nathanpower1/3D_Printed_Spectrometer/New Spectrometer Spectral Pics/mercury new spec 3.png

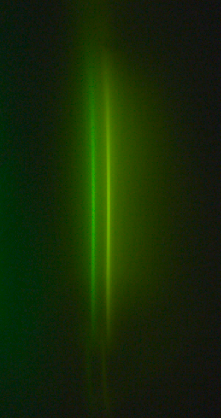
New Spectrometer Spectral Pics/mercury new spec 3.png
