nathanpower1/3D_Printed_Spectrometer/New Spectrometer Spectral Pics/mercury new spectometer.png

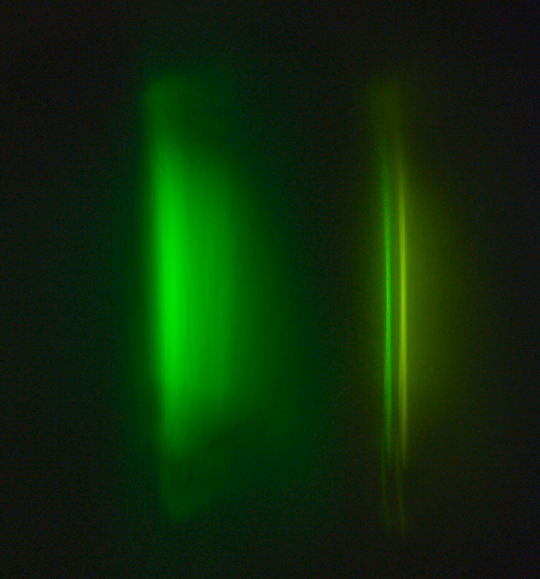
New Spectrometer Spectral Pics/mercury new spectometer.png
