nathanpower1/3D_Printed_Spectrometer/New Spectrometer Spectral Pics/Mercury Plot New.png

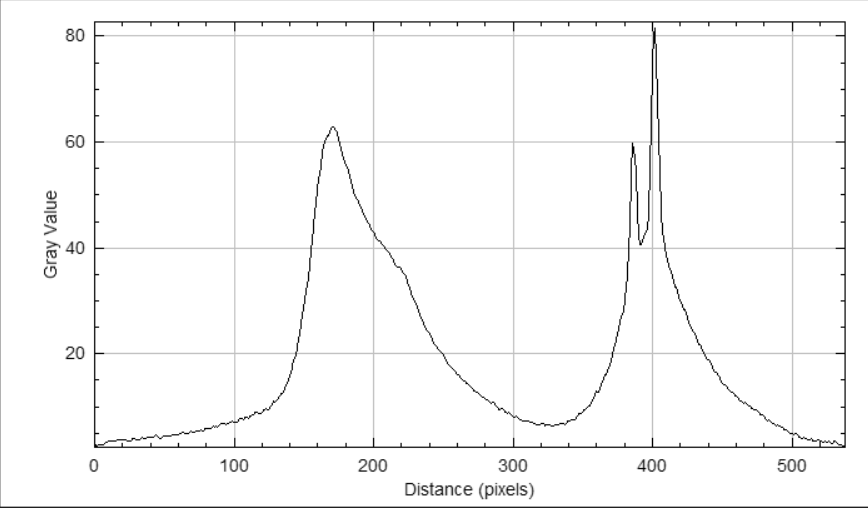
New Spectrometer Spectral Pics/Mercury Plot New.png
