nathanpower1/3D_Printed_Spectrometer/New Spectrometer Spectral Pics/neon new spec 2.png

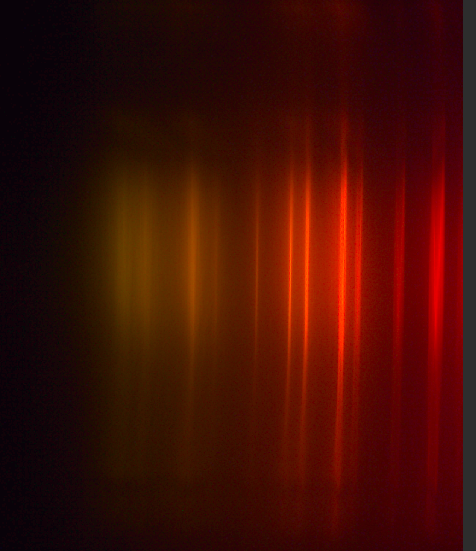
New Spectrometer Spectral Pics/neon new spec 2.png
