nathanpower1/3D_Printed_Spectrometer/New Spectrometer Spectral Pics/neon new spec.png

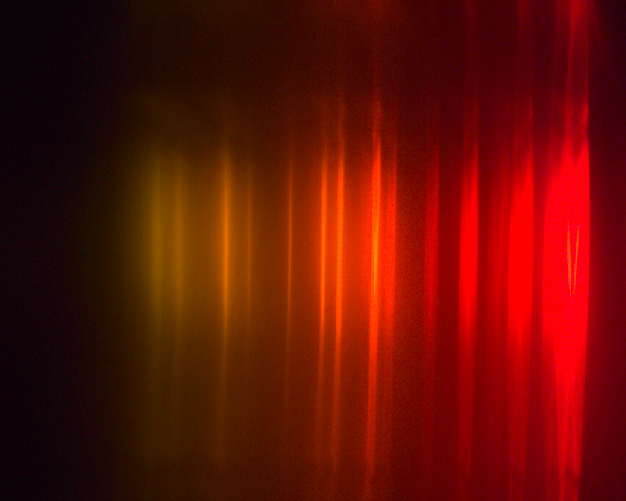
New Spectrometer Spectral Pics/neon new spec.png
