nathanpower1/3D_Printed_Spectrometer/New Spectrometer Spectral Pics/Neon Plot New.png

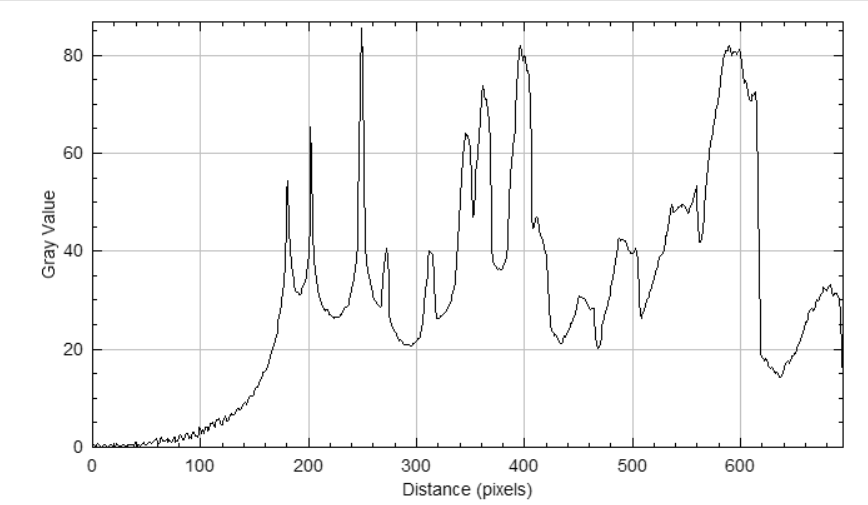
New Spectrometer Spectral Pics/Neon Plot New.png
