nathanpower1/3D_Printed_Spectrometer/New Spectrometer Spectral Pics/sodium doublet new spec 2.png

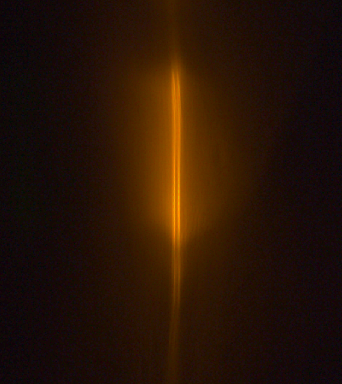
New Spectrometer Spectral Pics/sodium doublet new spec 2.png
