nathanpower1/3D_Printed_Spectrometer/3D Printer Files/SlitFiles/FixedBlade.stl

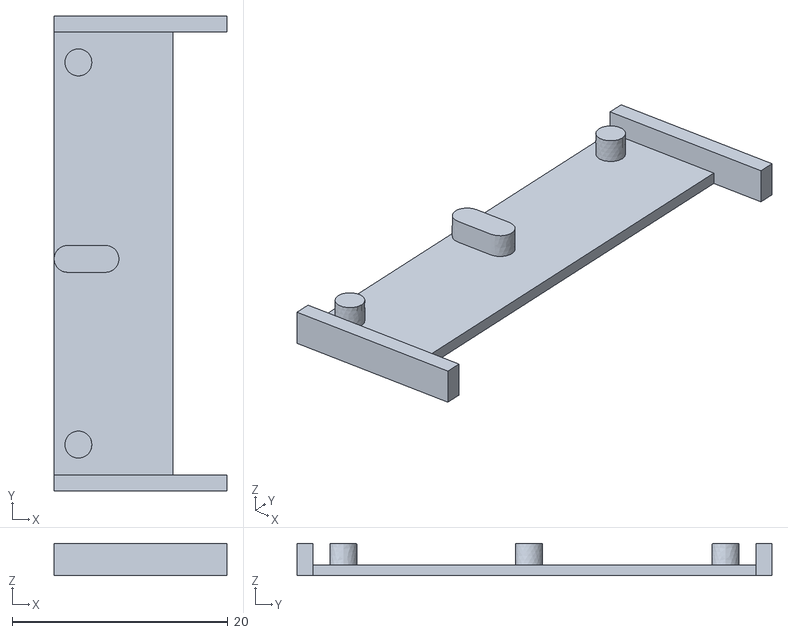
[picture p31: CAD file, 2024-04-24]
3D Printer Files/SlitFiles/FixedBlade.stl
16.0 x 44.0 x 3.00
