nathanpower1/3D_Printed_Spectrometer/3D Printer Files/CamFiles/Camera v2.stl

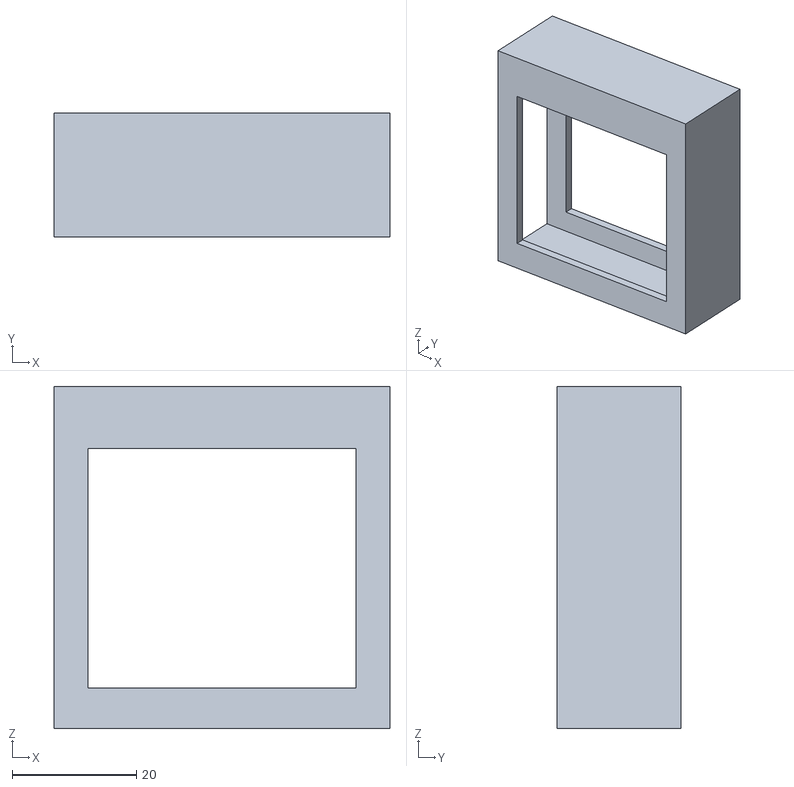
[picture p32: CAD file, 2024-04-24]
3D Printer Files/CamFiles/Camera v2.stl
54.0 x 20.0 x 55.0
