nathanpower1/3D_Printed_Spectrometer/3D Printer Files/Lens CAD file/Customizable_Optical_Lens_Holder_3359613/files/lense_holder_110x18.stl

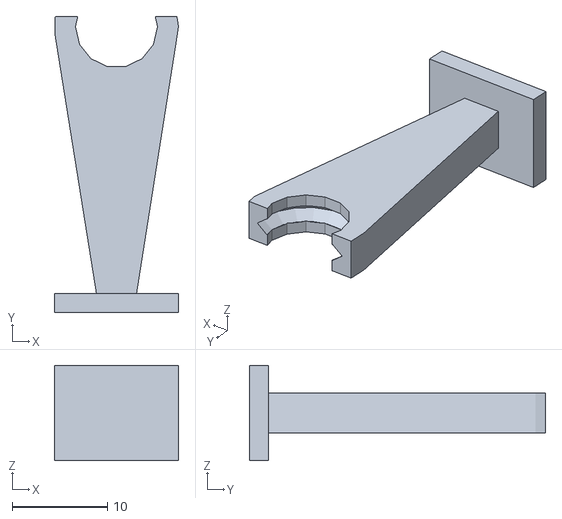
[picture p33: CAD file, 2024-04-24]
3D Printer Files/Lens CAD file/Customizable_Optical_Lens_Holder_3359613/files/lense_holder_110x18.stl
13.0 x 31.1 x 10.0
