nathanpower1/3D_Printed_Spectrometer/3D Printer Files/CamFiles/Case v1 Nathan Power.stl

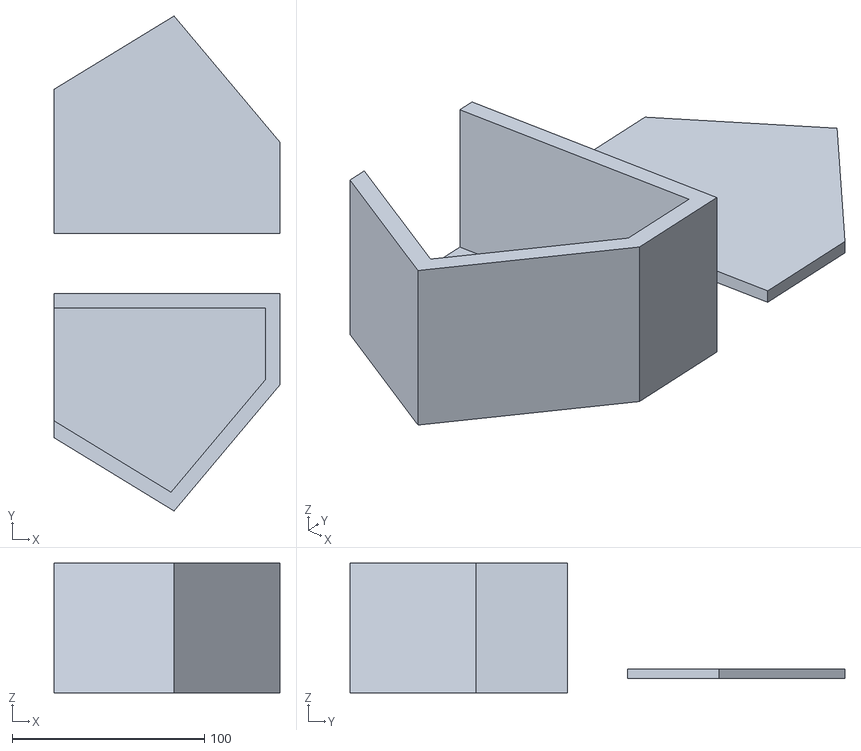
[picture p34: CAD file, 2024-04-24]
3D Printer Files/CamFiles/Case v1 Nathan Power.stl
117.5 x 257.5 x 67.5
