nathanpower1/3D_Printed_Spectrometer/3D Print Spectral Pics/3D print.jpg

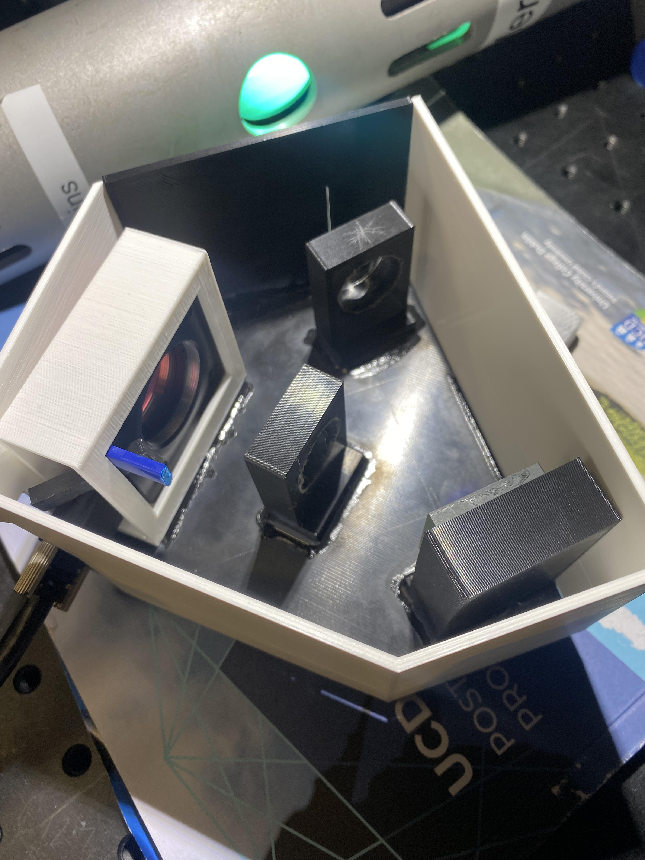
3D Print Spectral Pics/3D print.jpg
