nathanpower1/3D_Printed_Spectrometer/3D Print Spectral Pics/CamScanner 04-14-2023 22.21_1.jpg

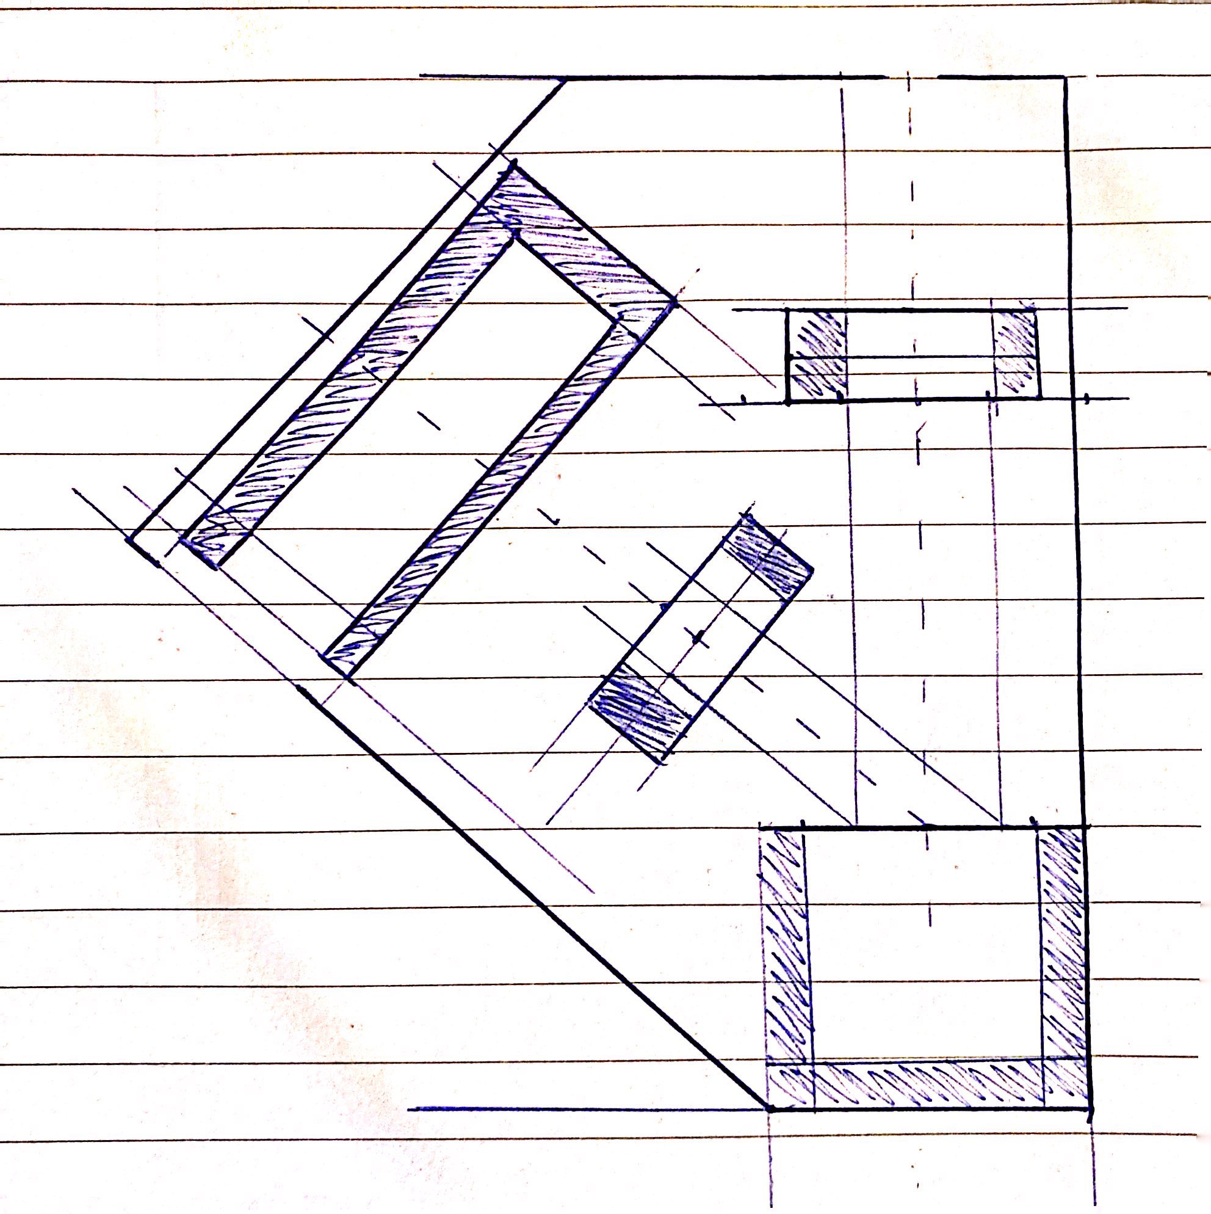
3D Print Spectral Pics/CamScanner 04-14-2023 22.21_1.jpg
