nathanpower1/3D_Printed_Spectrometer/3D Print Spectral Pics/final.jpg

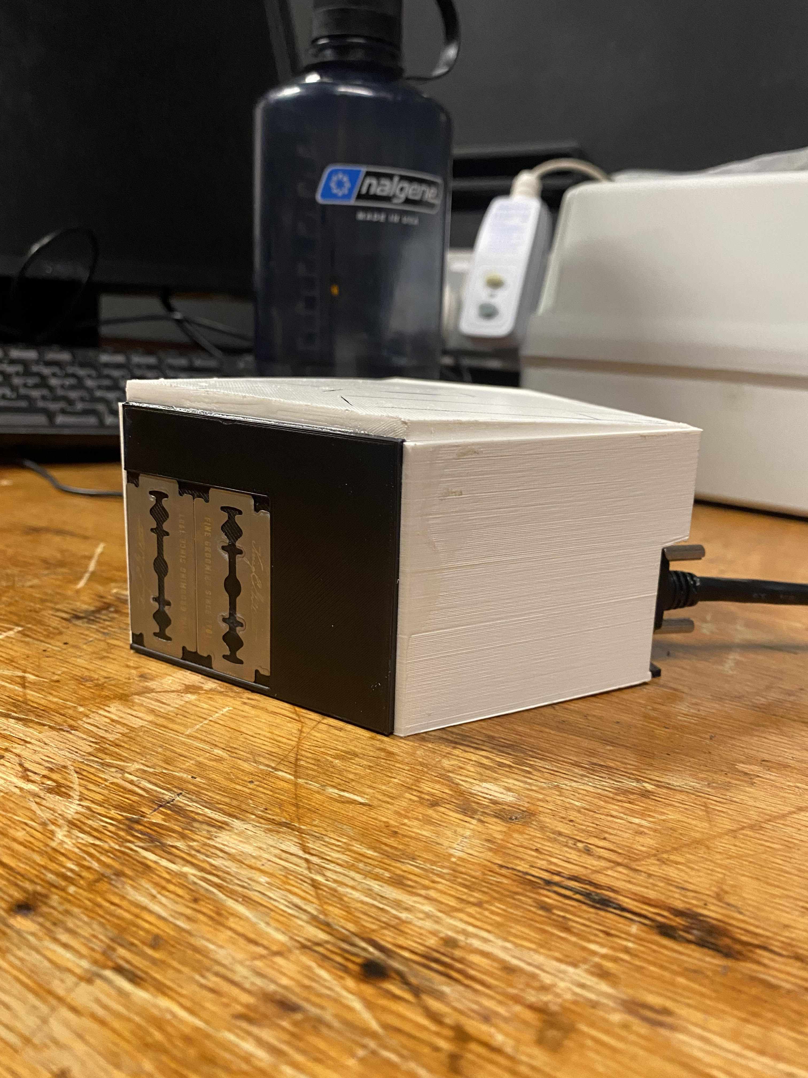
3D Print Spectral Pics/final.jpg
