nathanpower1/3D_Printed_Spectrometer/3D Print Spectral Pics/mercury pic.png

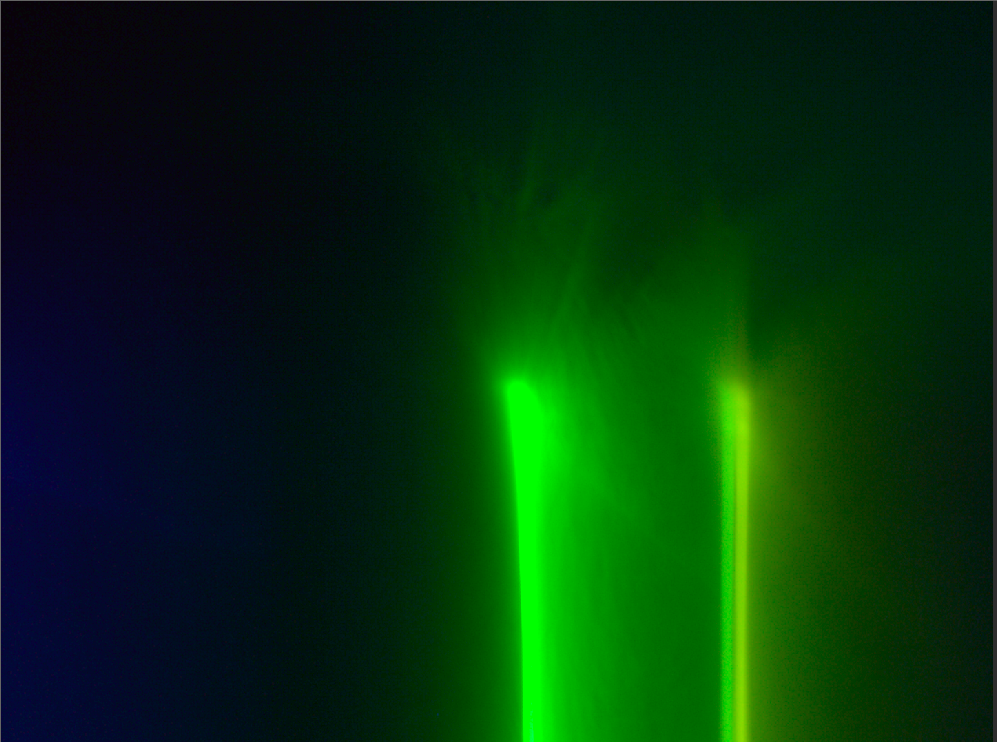
3D Print Spectral Pics/mercury pic.png
