nathanpower1/3D_Printed_Spectrometer/3D Print Spectral Pics/Mercury Plot.png

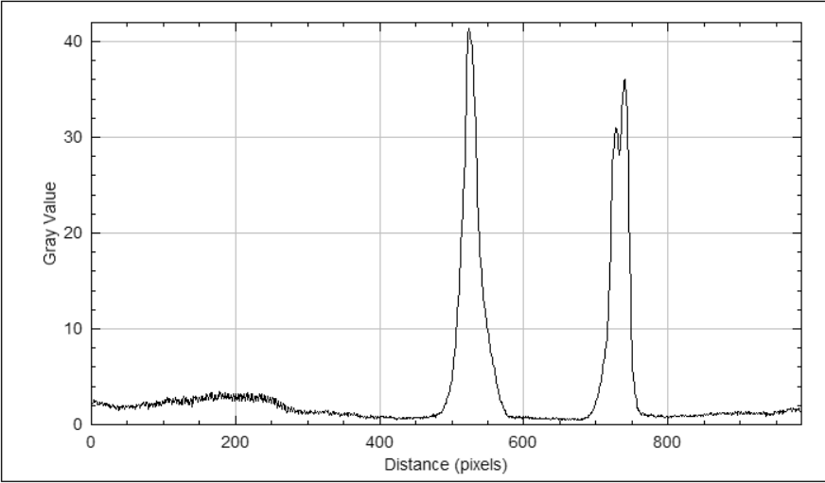
3D Print Spectral Pics/Mercury Plot.png
