nathanpower1/3D_Printed_Spectrometer/3D Print Spectral Pics/slit.jpg

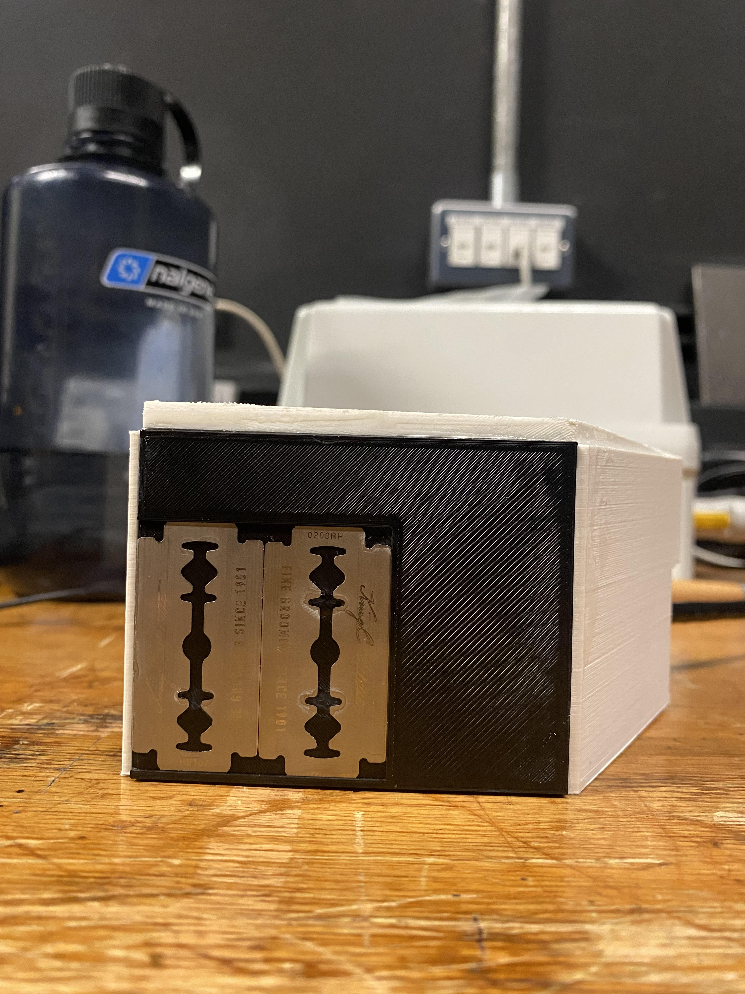
3D Print Spectral Pics/slit.jpg
