nathanpower1/3D_Printed_Spectrometer/3D Print Spectral Pics/white light.png

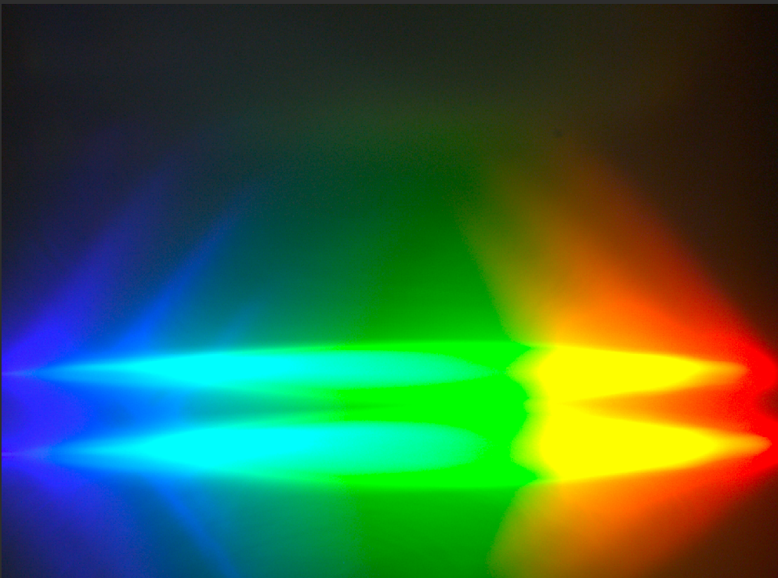
3D Print Spectral Pics/white light.png
