nathanpower1/3D_Printed_Spectrometer/3D Printer Files/GratingFiles/grating.png

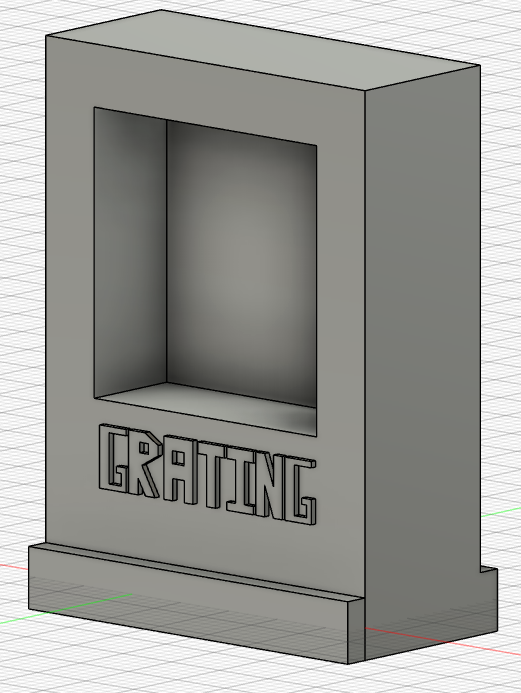
3D Printer Files/GratingFiles/grating.png
