nathanpower1/3D_Printed_Spectrometer/3D Printer Files/Lens CAD file/lens holder.png

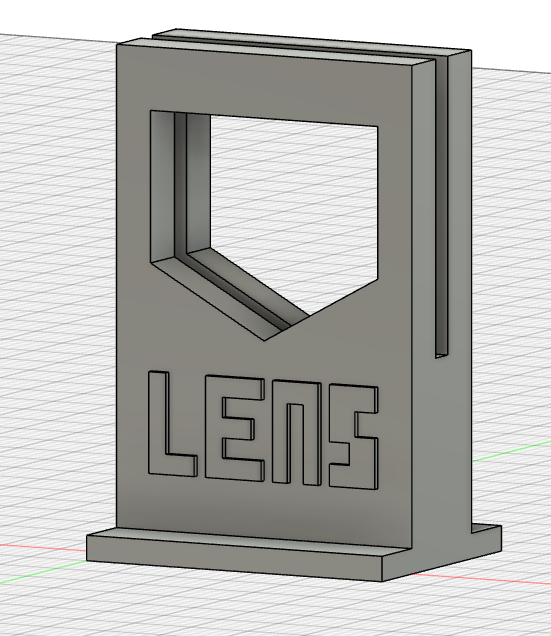
3D Printer Files/Lens CAD file/lens holder.png
